kyobg/HOOF-IMU/vision/Horse Pictures/HV10-2.png

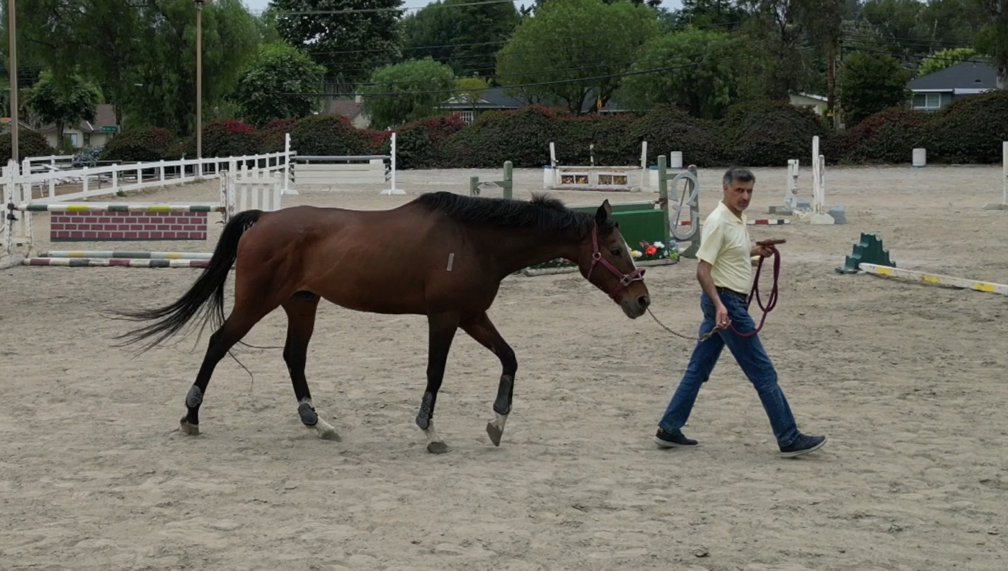
vision/Horse Pictures/HV10-2.png
