kyobg/HOOF-IMU/vision/Masks/HV10_M3_LAB_Binary.png

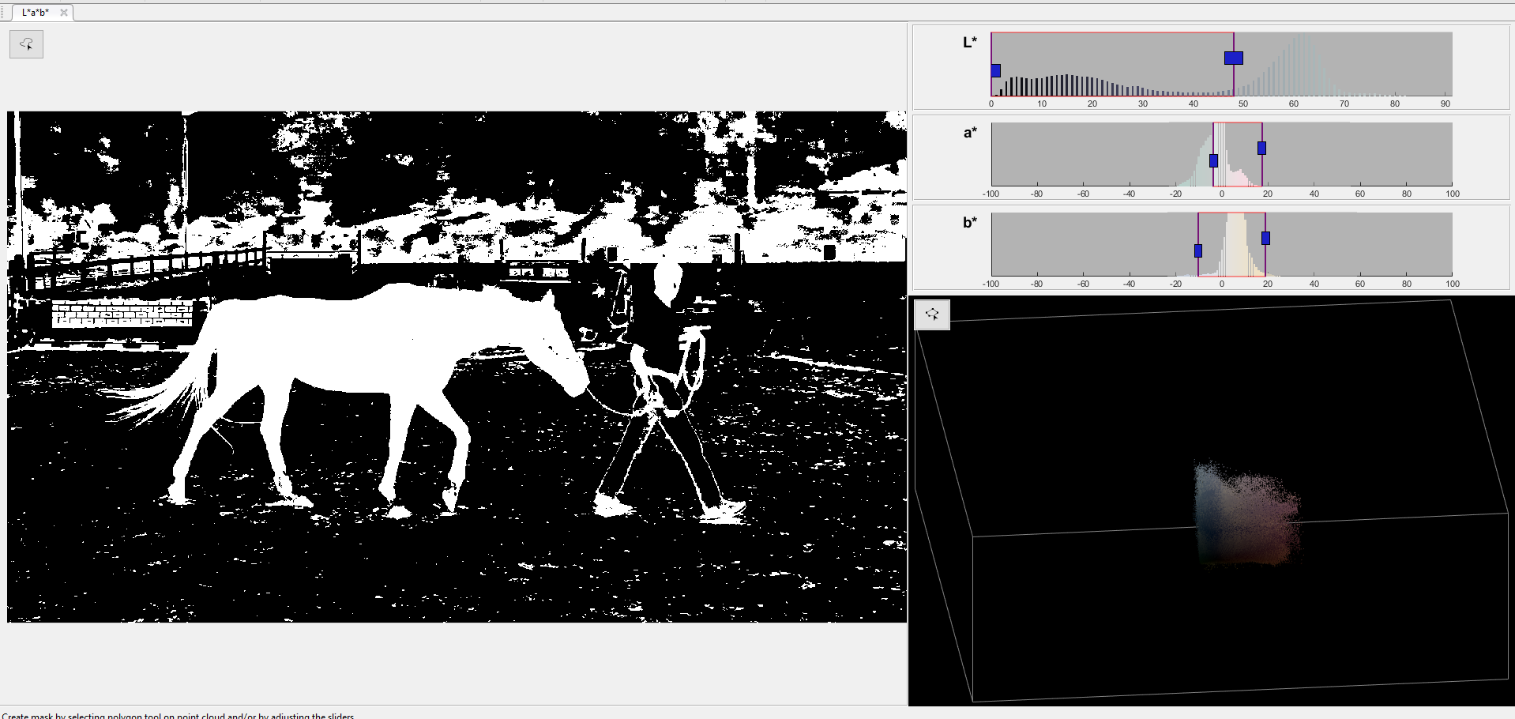
vision/Masks/HV10_M3_LAB_Binary.png
